batkay/Lightsaber/SpiceSimulations/button.asc

C1: Cap; 1µ
R1: Res; 10k
R5: Res; 1k
V1: battery; 5
Named nets: 0, c
.tran 1m 100m
.ic V(c)=0
