batkay/Lightsaber/SpiceSimulations/ship mode.asc

C1: Cap; 1µ
M1: pmos
R1: Res; 2k
R2: Res; 10k
S1: sw
V1: voltage; 5
Named nets: 0
.model SW SW(Ron=1 Roff=1Meg Vt=2.5 Vh=-.4)
.tran .1 1
