batkay/Lightsaber/Firmware/Core/Inc/sound.h

/*
 * sound.h
 *
 *  Created on: Aug 7, 2024
 *      Author: thomas
 */

#ifndef INC_SOUND_H_
#define INC_SOUND_H_
// Array that stores the 8 bit values of a lightsaber sound file
char swing[] = {
		0x80,
		0x80,
		0x7f,
		0x80,
		0x7f,
		0x80,
		0x7f,
		0x80,
		0x7f,
		0x80,
		0x7f,
		0x80,
		0x7f,
		0x7f,
		0x7f,
		0x7e,
		0x7f,
		0x7e,
		0x7f,
		0x7e,
		0x7f,
		0x7e,
		0x7f,
		0x7f,
		0x7f,
		0x7f,
		0x7f,
		0x7f,
		0x7f,
		0x7f,
		0x7f,
		0x7f,
		0x7f,
		0x7f,
		0x7f,
		0x7f,
		0x7f,
		0x7e,
		0x7f,
		0x7f,
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

};


#endif /* INC_SOUND_H_ */
